pdxjohnny/flextimus-prime/include/stdint.h

#ifndef _STDINT_H
#define _STDINT_H

#define NULL      0
#define true      1
#define false     0

typedef char int8_t;
typedef unsigned char uint8_t;
typedef short int16_t;
typedef unsigned short uint16_t;
typedef int int32_t;
typedef unsigned int uint32_t;

typedef uint8_t bool;

#endif /* _STDINT_H */
